AleReb/HIRI_ESTACIONARIO_CALEFACTOR/HIRI_STATIC_CALEFACTOR_0_1/serial_commands.ino

// -------------------- Serial Commands --------------------
// Sistema de comandos seriales para debug y mantenimiento
// Uso: Enviar comando por serial monitor (115200 baud, newline)
// Ejemplo: "help" → muestra lista de comandos

#include "config.h"

extern SystemConfig config;
extern TinyGsm modem;
extern RTC_DS3231 rtc;
extern Preferences prefs;
extern bool rtcOK;
extern bool SDOK;
extern bool loggingEnabled;
extern bool streaming;
extern bool oledOK;
extern uint32_t sendCounter;
extern uint32_t sdSaveCounter;
extern String csvFileName;
extern String rebootReason;
extern String networkOperator;
extern String networkTech;
extern String signalQuality;
extern String registrationStatus;
extern float batV;
extern int csq;
extern String gpsStatus;
extern String satellitesStr;
extern String hdopStr;
extern const char *DEVICE_ID_STR;
extern String VERSION;
extern String logFilePath;
extern String failedTxPath;

// Forward declarations
void saveConfig();
void configSetDefaults();
void printConfig();
void applyLEDConfig();
void clearSDCard();
void printSDInfo();
void printSDFileList();
String generateCSVFileName();
void writeCSVHeader();
bool syncRtcFromModem();      // Assuming implemented or needed
void resetModemSyncCounter(); // Assuming implemented or needed
bool getModemEpoch(uint32_t &epoch);

// Procesa comandos por puerto serie para operación, diagnóstico y mantenimiento.
// Permite inspección y control en campo sin recompilar firmware.
void processSerialCommand() {
  if (!Serial.available())
    return;

  String cmd = Serial.readStringUntil('\n');
  cmd.trim();
  cmd.toLowerCase();

  if (cmd.length() == 0)
    return;

  Serial.println("\n>>> Command: " + cmd);

  // -------------------- HELP --------------------
  if (cmd == "help" || cmd == "?") {
    Serial.println(F("=== HIRI PRO Serial Commands ==="));
    Serial.println(F("\n[RTC/Time]"));
    Serial.println(F("  rtc         - Show current RTC time"));
    Serial.println(F("  rtcsync     - Force sync RTC with modem"));
    Serial.println(F("  modemtime   - Show modem time only"));

    Serial.println(F("\n[Counters]"));
    Serial.println(F("  counters    - Show SD/HTTP counters"));
    Serial.println(F("  resetcnt    - Reset both counters to 0"));
    Serial.println(F("  stats       - Show detailed statistics"));

    Serial.println(F("\n[SD Card]"));
    Serial.println(F("  sdinfo      - Show SD card info"));
    Serial.println(F("  sdlist      - List files on SD"));
    Serial.println(F("  sdnew       - Create new CSV file"));
    Serial.println(
        F("  sdclear     - Delete all files on SD (WARNING: irreversible!)"));

    Serial.println(F("\n[Network/Modem]"));
    Serial.println(F("  netinfo     - Show network info"));
    Serial.println(F("  csq         - Show signal quality"));

    Serial.println(F("\n[System]"));
    Serial.println(F("  sysinfo     - Show system info"));
    Serial.println(F("  reboot      - Reboot ESP32"));
    Serial.println(F("  mem         - Show memory usage"));
    Serial.println(F("  cal <1-300> - Prueba el calefactor por N segundos (corte a 70 C)"));
    Serial.println(F("                 Ejemplo: cal 120"));

    Serial.println(F("\n[Streaming]"));
    Serial.println(F("  start       - Start streaming"));
    Serial.println(F("  stop        - Stop streaming"));

    Serial.println(F("\n[UI / OLED Flow]"));
    Serial.println(F("  Vista: Plantower / calefactor / sistema / GPS opcional"));
    Serial.println(F("  BTN1: prueba HTTP + SD + calefactor por 10 s"));
    Serial.println(F("  BTN2: siguiente vista (deshabilitado si BUTTON_PIN_2=-1)"));

    Serial.println(F("\n[Configuration]"));
    Serial.println(F("  config              - Show all configuration"));
    Serial.println(F("  config sd/http/display/power/system - Show specific config"));
    Serial.println(F("  set sdauto on/off   - Mount SD on boot"));
    Serial.println(F("  set sdsave 3/60/600/1200 - SD save period (seconds)"));
    Serial.println(F("  set httpsend 3/60/600/1200 - HTTP send period (seconds)"));
    Serial.println(F("  set httptimeout 5-30 - HTTP timeout (seconds)"));
    Serial.println(F("  set oledoff on/off  - OLED auto-off"));
    Serial.println(F("  set oledtime 60/120/180 - OLED timeout (seconds)"));
    Serial.println(F("  set led on/off      - Enable NeoPixel"));
    Serial.println(F("  set ledbright 10/25/50/100 - LED brightness (%)"));
    Serial.println(F("  set autostart on/off - Autostart streaming on boot"));
    Serial.println(F("  set gnss on/off     - Enable or disable GNSS subsystem"));
    Serial.println(F("  set autowaitgps on/off - Wait GPS fix before start"));
    Serial.println(
        F("  set autogpsto 60-900 - GPS timeout (60s-15min, default: 600s)"));
    Serial.println(F("  set rotatedisplay on/off - Rotate display 180 deg"));
    Serial.println(F("  set reboot 0-720   - Auto reboot hours (0 disables, default 3)"));
    Serial.println(
        F("  set gnssmode 1/3/5/7/15 - GNSS mode (1=GPS, 3=GPS+GLO, 15=ALL)"));
    Serial.println(F("  configreset         - Reset to defaults"));
    Serial.println(F("  configsave          - Save config to flash"));

    Serial.println(F("\n"));
  }

  // -------------------- HEATER COMMANDS --------------------
  else if (cmd.startsWith("cal ") || cmd.startsWith("cal.")) {
    String secondsText = cmd.substring(4);
    if (!heaterRequestTimedTest(secondsText)) {
      Serial.println(F("[CALEFACTOR] Uso: cal <1-300>. Ejemplo: cal 120"));
    }
  }

  // -------------------- RTC COMMANDS --------------------
  else if (cmd == "rtc") {
    if (!rtcOK) {
      Serial.println("[RTC] Not available");
      return;
    }
    DateTime now = rtc.now();
    Serial.printf("[RTC] Current time: %04d-%02d-%02d %02d:%02d:%02d\n",
                  now.year(), now.month(), now.day(), now.hour(), now.minute(),
                  now.second());
    Serial.printf("[RTC] Epoch: %lu\n", (unsigned long)now.unixtime());
    Serial.printf("[RTC] Temperature: %.2f°C\n", rtc.getTemperature());
    // Serial.printf("[RTC] Modem syncs: %u/3\n", rtcModemSyncCount);
  }  
  else if (cmd == "rtcsync") {
    if (!rtcOK) {
      Serial.println("[RTC] Not available");
      return;
    }
     Serial.printf("[RTC] Modem syncs: %u/3\n", rtcModemSyncCount);
    if (syncRtcFromModem()) {
      Serial.println("[RTC] ✓ Synced from modem");
    } else {
      Serial.println("[RTC] ✗ Sync failed");
    }
   
  }
  else if (cmd == "modemtime") {
    uint32_t epoch = 0;
    if (getModemEpoch(epoch)) {
      DateTime dt(epoch);
      Serial.printf("[MODEM] Current time: %04d-%02d-%02d %02d:%02d:%02d\n",
                    dt.year(), dt.month(), dt.day(), dt.hour(), dt.minute(), dt.second());
    } else {
      Serial.println("[MODEM] ✗ Failed to get time");
    }
  }

  // -------------------- COUNTER COMMANDS --------------------
  else if (cmd == "counters") {
    Serial.println("=== Counters ===");
    Serial.printf("SD saves:     %lu\n", (unsigned long)sdSaveCounter);
    Serial.printf("HTTP success: %lu\n", (unsigned long)sendCounter);
    if (sdSaveCounter > 0) {
      float successRate = (float)sendCounter / (float)sdSaveCounter * 100.0f;
      Serial.printf("Success rate: %.1f%%\n", successRate);
    }
  }

  else if (cmd == "resetcnt") {
    Serial.println("[COUNTERS] Resetting to 0...");
    sendCounter = 0;
    sdSaveCounter = 0;
    prefs.begin("system", false);
    prefs.putUInt("sendCnt", 0);
    prefs.putUInt("sdCnt", 0);
    prefs.end();
    Serial.println("[COUNTERS] ✓ Reset complete");
  }

  else if (cmd == "stats") {
    Serial.println("=== System Statistics ===");
    Serial.printf("Version:      %s\n", VERSION.c_str());
    Serial.printf("Device ID:    %s\n", DEVICE_ID_STR);
    Serial.printf("Uptime:       %lu s\n", millis() / 1000);
    Serial.printf("Streaming:    %s\n", streaming ? "ON" : "OFF");
    Serial.printf("SD logging:   %s\n", loggingEnabled ? "ON" : "OFF");
    Serial.printf("SD saves:     %lu\n", (unsigned long)sdSaveCounter);
    Serial.printf("HTTP success: %lu\n", (unsigned long)sendCounter);
    if (sdSaveCounter > 0) {
      float successRate = (float)sendCounter / (float)sdSaveCounter * 100.0f;
      Serial.printf("Success rate: %.1f%%\n", successRate);
    }
    Serial.printf("Battery:      %.2fV\n", batV);
    Serial.printf("CSQ:          %d\n", csq);
    Serial.printf("GPS:          %s\n", gpsStatus.c_str());
    Serial.printf("Satellites:   %s\n", satellitesStr.c_str());
    Serial.printf("HDOP:         %s\n", hdopStr.c_str());
    Serial.printf("Reboot reason:%s\n", rebootReason.c_str());
  }

  // -------------------- SD COMMANDS --------------------
  else if (cmd == "sdinfo") {
    printSDInfo();
  }

  else if (cmd == "sdlist") {
    printSDFileList();
  }

  else if (cmd == "sdnew") {
    if (!SDOK) {
      Serial.println("[SD] Not available");
      return;
    }
    Serial.println("[SD] Creating new CSV file...");
    csvFileName = generateCSVFileName();
    writeCSVHeader();
    Serial.printf("[SD] ✓ New file created: %s\n", csvFileName.c_str());
    // Persist new filename
    prefs.begin("system", false);
    prefs.putString("csvFile", csvFileName);
    prefs.end();
  }

  else if (cmd == "sdclear") {
    if (!SDOK) {
      Serial.println("[SD] Not available");
      return;
    }
    Serial.println(
        "[SD] ⚠ WARNING: This will delete ALL files on the SD card!");
    Serial.println("[SD] Type 'sdclear confirm' to proceed");
  }

  else if (cmd == "sdclear confirm") {
    clearSDCard();
  }

  // -------------------- NETWORK COMMANDS --------------------
  else if (cmd == "netinfo") {
    Serial.println("=== Network Info ===");
    Serial.printf("Operator:     %s\n", networkOperator.c_str());
    Serial.printf("Technology:   %s\n", networkTech.c_str());
    Serial.printf("CSQ:          %d\n", csq);
    Serial.printf("Registration: %s\n", registrationStatus.c_str());
    Serial.printf("PDP connected:%s\n", modem.isGprsConnected() ? "YES" : "NO");
    Serial.printf("Network conn: %s\n",
                  modem.isNetworkConnected() ? "YES" : "NO");
  }

  else if (cmd == "csq") {
    int newCsq = modem.getSignalQuality();
    Serial.printf("[MODEM] Signal Quality: %d", newCsq);
    if (newCsq == 0)
      Serial.println(" (no signal)");
    else if (newCsq < 10)
      Serial.println(" (marginal)");
    else if (newCsq < 15)
      Serial.println(" (ok)");
    else if (newCsq < 20)
      Serial.println(" (good)");
    else
      Serial.println(" (excellent)");
  }

  // -------------------- SYSTEM COMMANDS --------------------
  else if (cmd == "sysinfo") {
    Serial.println("=== System Info ===");
    Serial.printf("Firmware:     %s\n", VERSION.c_str());
    Serial.printf("Device ID:    %s\n", DEVICE_ID_STR);
    Serial.printf("Chip model:   %s\n", ESP.getChipModel());
    Serial.printf("Chip cores:   %d\n", ESP.getChipCores());
    Serial.printf("CPU freq:     %d MHz\n", ESP.getCpuFreqMHz());
    Serial.printf("Flash size:   %lu MB\n",
                  ESP.getFlashChipSize() / (1024 * 1024));
    Serial.printf("Free heap:    %lu bytes\n", ESP.getFreeHeap());
    Serial.printf("Uptime:       %lu s\n", millis() / 1000);
    if (config.scheduledRebootHours == 0) {
      Serial.println("Auto reboot:  OFF");
    } else {
      uint32_t uptimeS = millis() / 1000UL;
      uint32_t intervalS = (uint32_t)config.scheduledRebootHours * 3600UL;
      uint32_t remainingS = uptimeS < intervalS ? intervalS - uptimeS : 0;
      Serial.printf("Auto reboot:  every %u h, next in %lu s\n",
                    config.scheduledRebootHours, remainingS);
    }
    Serial.printf("Reboot reason:%s\n", rebootReason.c_str());
  }

  else if (cmd == "mem") {
    Serial.println("=== Memory Usage ===");
    Serial.printf("Free heap:    %lu bytes\n", ESP.getFreeHeap());
    Serial.printf("Heap size:    %lu bytes\n", ESP.getHeapSize());
    Serial.printf("Min free heap:%lu bytes\n", ESP.getMinFreeHeap());
    Serial.printf("Max alloc:    %lu bytes\n", ESP.getMaxAllocHeap());
  }

  else if (cmd == "reboot") {
    Serial.println("[SYSTEM] Rebooting in 2 seconds...");
    delay(2000);
    ESP.restart();
  }

  // -------------------- STREAMING COMMANDS --------------------
  else if (cmd == "start") {
    if (streaming) {
      Serial.println("[STREAM] Already running");
    } else {
      Serial.println("[STREAM] Starting via serial command...");
      streaming = true;
      // Etapa de integración: iniciar transmisión con logging OFF.
      loggingEnabled = false;
      Serial.printf("[STREAM] ✓ Started (SD logging: %s)\n",
                    loggingEnabled ? "ON" : "OFF");
    }
  }

  else if (cmd == "stop") {
    if (!streaming) {
      Serial.println("[STREAM] Already stopped");
    } else {
      Serial.println("[STREAM] Stopping...");
      streaming = false;
      loggingEnabled = false;
      Serial.println("[STREAM] ✓ Stopped");
    }
  }

  // -------------------- CONFIGURATION COMMANDS --------------------
  else if (cmd == "config") {
    printConfig();
  }

  else if (cmd == "config sd") {
    Serial.println("=== SD Configuration ===");
    Serial.printf("Auto-mount on boot: %s\n",
                  config.sdAutoMount ? "ON" : "OFF");
    Serial.printf("Save period:        %lu ms (%lu s)\n", config.sdSavePeriod,
                  config.sdSavePeriod / 1000);
  }

  else if (cmd == "config http") {
    Serial.println("=== HTTP Configuration ===");
    Serial.printf("Send period: %lu ms (%lu s)\n", config.httpSendPeriod,
                  config.httpSendPeriod / 1000);
    Serial.printf("Timeout:     %u seconds\n", config.httpTimeout);
  }

  else if (cmd == "config display") {
    Serial.println("=== Display Configuration ===");
    Serial.printf("Auto-off: %s\n", config.oledAutoOff ? "ON" : "OFF");
    Serial.printf("Timeout:  %lu ms (%lu s)\n", config.oledTimeout,
                  config.oledTimeout / 1000);
  }

  else if (cmd == "config power") {
    Serial.println("=== Power/LED Configuration ===");
    Serial.printf("NeoPixel enabled: %s\n", config.ledEnabled ? "YES" : "NO");
    Serial.printf("Brightness:       %u%%\n", config.ledBrightness);
  }

  else if (cmd == "config system") {
    Serial.println("=== System Configuration ===");
    Serial.printf("Rotate display:   %s\n", config.rotateDisplay ? "YES" : "NO");
    if (config.scheduledRebootHours == 0) {
      Serial.println("Scheduled reboot: OFF");
    } else {
      Serial.printf("Scheduled reboot: every %u hours\n",
                    config.scheduledRebootHours);
    }
  }

  else if (cmd.startsWith("set ")) {
    String param = cmd.substring(4);
    param.trim();

    // SD auto-mount
    if (param == "sdauto on") {
      config.sdAutoMount = true;
      saveConfig();
      Serial.println("[CONFIG] SD auto-mount: ON (will mount on next boot)");
    } else if (param == "sdauto off") {
      config.sdAutoMount = false;
      saveConfig();
      Serial.println("[CONFIG] SD auto-mount: OFF");
    }

    // SD save period
    else if (param == "sdsave 3") {
      config.sdSavePeriod = 3000;
      saveConfig();
      Serial.println("[CONFIG] SD save period: 3 seconds");
    } else if (param == "sdsave 60") {
      config.sdSavePeriod = 60000;
      saveConfig();
      Serial.println("[CONFIG] SD save period: 60 seconds");
    } else if (param == "sdsave 600") {
      config.sdSavePeriod = 600000;
      saveConfig();
      Serial.println("[CONFIG] SD save period: 600 seconds (10 min)");
    } else if (param == "sdsave 1200") {
      config.sdSavePeriod = 1200000;
      saveConfig();
      Serial.println("[CONFIG] SD save period: 1200 seconds (20 min)");
    }

    // HTTP send period
    else if (param == "httpsend 3") {
      config.httpSendPeriod = 3000;
      saveConfig();
      Serial.println("[CONFIG] HTTP send period: 3 seconds");
    } else if (param == "httpsend 60") {
      config.httpSendPeriod = 60000;
      saveConfig();
      Serial.println("[CONFIG] HTTP send period: 60 seconds");
    } else if (param == "httpsend 600") {
      config.httpSendPeriod = 600000;
      saveConfig();
      Serial.println("[CONFIG] HTTP send period: 600 seconds (10 min)");
    } else if (param == "httpsend 1200") {
      config.httpSendPeriod = 1200000;
      saveConfig();
      Serial.println("[CONFIG] HTTP send period: 1200 seconds (20 min)");
    }

    // HTTP timeout
    else if (param.startsWith("httptimeout ")) {
      int timeout = param.substring(12).toInt();
      if (timeout >= 5 && timeout <= 30) {
        config.httpTimeout = timeout;
        saveConfig();
        Serial.printf("[CONFIG] HTTP timeout: %d seconds\n", timeout);
      } else {
        Serial.println("[CONFIG] ✗ Timeout must be 5-30 seconds");
      }
    }

    // OLED auto-off
    else if (param == "oledoff on") {
      config.oledAutoOff = true;
      saveConfig();
      Serial.println("[CONFIG] OLED auto-off: ON");
    } else if (param == "oledoff off") {
      config.oledAutoOff = false;
      saveConfig();
      // Enable power
      // u8g2.setPowerSave(0); // Extern not available here directly, will
      // handle loop
      Serial.println("[CONFIG] OLED auto-off: OFF (always on)");
    }

    // OLED timeout
    else if (param == "oledtime 60") {
      config.oledTimeout = 60000;
      saveConfig();
      Serial.println("[CONFIG] OLED timeout: 60 seconds");
    } else if (param == "oledtime 120") {
      config.oledTimeout = 120000;
      saveConfig();
      Serial.println("[CONFIG] OLED timeout: 120 seconds (2 min)");
    } else if (param == "oledtime 180") {
      config.oledTimeout = 180000;
      saveConfig();
      Serial.println("[CONFIG] OLED timeout: 180 seconds (3 min)");
    }

    // LED enable/disable
    else if (param == "led on") {
      config.ledEnabled = true;
      saveConfig();
      applyLEDConfig();
      Serial.println("[CONFIG] NeoPixel: ON");
    } else if (param == "led off") {
      config.ledEnabled = false;
      saveConfig();
      applyLEDConfig();
      Serial.println("[CONFIG] NeoPixel: OFF");
    }

    // LED brightness
    else if (param == "ledbright 10") {
      config.ledBrightness = 10;
      saveConfig();
      applyLEDConfig();
      Serial.println("[CONFIG] LED brightness: 10%");
    } else if (param == "ledbright 25") {
      config.ledBrightness = 25;
      saveConfig();
      applyLEDConfig();
      Serial.println("[CONFIG] LED brightness: 25%");
    } else if (param == "ledbright 50") {
      config.ledBrightness = 50;
      saveConfig();
      applyLEDConfig();
      Serial.println("[CONFIG] LED brightness: 50%");
    } else if (param == "ledbright 100") {
      config.ledBrightness = 100;
      saveConfig();
      applyLEDConfig();
      Serial.println("[CONFIG] LED brightness: 100%");
    }

    // Autostart
    else if (param == "autostart on") {
      config.autostart = true;
      saveConfig();
      Serial.println("[CONFIG] Autostart: ON (will start on next boot)");
    } else if (param == "autostart off") {
      config.autostart = false;
      saveConfig();
      Serial.println("[CONFIG] Autostart: OFF");
    }

    else if (param == "gnss on") {
      config.gnssEnabled = true;
      saveConfig();
      Serial.println("[CONFIG] GNSS: ON (requires reboot)");
    } else if (param == "gnss off") {
      config.gnssEnabled = false;
      saveConfig();
      Serial.println("[CONFIG] GNSS: OFF (requires reboot)");
    }

    // Autostart wait GPS
    else if (param == "autowaitgps on") {
      config.autostartWaitGps = true;
      saveConfig();
      Serial.println("[CONFIG] Autostart wait GPS: ON (will wait for fix)");
    } else if (param == "autowaitgps off") {
      config.autostartWaitGps = false;
      saveConfig();
      Serial.println("[CONFIG] Autostart wait GPS: OFF");
    }

    // Autostart GPS timeout
    else if (param.startsWith("autogpsto ")) {
      int val = param.substring(10).toInt();
      if (val >= 60 && val <= 900) {
        config.autostartGpsTimeout = val;
        saveConfig();
        Serial.printf("[CONFIG] Autostart GPS timeout: %u seconds (%u min)\n",
                      val, val / 60);
      } else {
        Serial.println(
            "[CONFIG] ✗ Invalid timeout (must be 60-900 seconds / 1-15 min)");
      }
    }

    // Rotate display
    else if (param == "rotatedisplay on") {
      config.rotateDisplay = true;
      saveConfig();
      if (oledOK) u8g2.setDisplayRotation(U8G2_R0);
      Serial.println("[CONFIG] Rotate Display: ON");
    } else if (param == "rotatedisplay off") {
      config.rotateDisplay = false;
      saveConfig();
      if (oledOK) u8g2.setDisplayRotation(U8G2_R2);
      Serial.println("[CONFIG] Rotate Display: OFF");
    }

    // Scheduled reboot
    else if (param.startsWith("reboot ")) {
      String valStr = param.substring(7);
      valStr.trim();
      bool numeric = valStr.length() > 0;
      for (size_t i = 0; i < valStr.length(); ++i) {
        if (!isDigit(valStr[i])) {
          numeric = false;
          break;
        }
      }

      int val = numeric ? valStr.toInt() : -1;
      if (val >= 0 && val <= 720) {
        config.scheduledRebootHours = (uint16_t)val;
        saveConfig();
        if (val == 0) {
          Serial.println("[CONFIG] Scheduled reboot: OFF");
        } else {
          Serial.printf("[CONFIG] Scheduled reboot: every %d hours\n", val);
        }
      } else {
        Serial.println("[CONFIG] Invalid reboot value (use 0-720 hours)");
      }
    }

    // GNSS mode
    else if (param.startsWith("gnssmode ")) {
      int val = param.substring(9).toInt();
      if (val == 1 || val == 3 || val == 5 || val == 7 || val == 15) {
        config.gnssMode = val;
        saveConfig();
        Serial.print("[CONFIG] GNSS mode: ");
        Serial.print(val);
        Serial.println(" (Requires Reboot)");
      } else {
        Serial.println("[CONFIG] ✗ Invalid mode (valid: 1, 3, 5, 7, 15)");
      }
    }

    else {
      Serial.println("[CONFIG] ✗ Unknown parameter. Type 'help' for list.");
    }
  }

  else if (cmd == "configreset") {
    Serial.println("[CONFIG] Resetting to defaults...");
    configSetDefaults();
    saveConfig();
    applyLEDConfig();
    Serial.println("[CONFIG] ✓ Reset complete. Reboot to apply all changes.");
  }

  else if (cmd == "configsave") {
    saveConfig();
  }

  // -------------------- UNKNOWN COMMAND --------------------
  else {
    Serial.println("[CMD] Unknown command. Type 'help' for list.");
  }

  Serial.println();
}
