AleReb/HIRI_ESTACIONARIO_CALEFACTOR/codigo_original/dfrobot_plantower_SD_sim7600V7/tipo.h

/*
  Fontname: -FontForge-MissingPlanet-Medium-R-Normal--72-690-75-75-P-272-ISO10646-1
  Copyright: Extant
  Glyphs: 91/423
  BBX Build Mode: 0
*/
const uint8_t MissingPlanet72[2692] U8G2_FONT_SECTION("MissingPlanet72") =
  "[\0\5\4\6\6\5\6\7\62\77\367\356)\356)\0\3\322\10+\12g \6\0\0\303+!\14E"
  "\12\301$\370\377\200\242\17(\42\13\216\3w)(D\377\37)#ZW\12\301-\251R!%\25R"
  "R!%\25RR!%\25RR!%\25R\312\3\377\1E\252THI\205\224THI\205\224T"
  "HI\205\224THI\205\224THI\205\224THI\205\224\362\300\177@\221*\25RR!%\25R"
  "R!%\25RR!%\25RR!\245\0$V\227\14\267m*\262\226\36\370\37)\251\220\222\12)"
  "\251\220\222\12)\251\220\222\12)\251\220\222\12)\251\220\222\12)\251\220\222\12)\351\201\377\200J\205\224"
  "THI\205\224THI\205\224THI\205\224THI\205\224THI\205\224THI\205<\360\277"
  "Td]\2%TW\12\301-p\344\1B\36 \344\1B\36 D\221B\24)D\221B\24)\344"
  "\1B\36 \344\1B\36 \344\1BJ+\262\346\222+\262\326\212\254\271\7\32y\200\220\7\10y\200"
  "\220\7\10)D\221B\24)D\221B\24y\200\220\7\10y\200\220\7\10q&p`\12A\62x\0"
  "\245\7Pz\0\245\7Pz\0\245\322J*\255\244\322J*\255\244\322J*\255\244\322J*\255\244\322"
  "*Rd!E\26Rd!E\272T\265\222J+\251\264\222J+\244\226\12\251R!U*\244*\211"
  "\270RZI\245\225TZI\245\225TP!\245\24TH)\5\25RJA\205\224\362\300 \17\244\366"
  "\0i\17\220\366\0i\5'\11\205\3\367$\370\3\12(\21N\12A)\370\227\352\377\377\377K\17\374"
  "\200\2)\21N\12A)\370\3*\325\377\377\377\227\36\370\3*(\327\5\345-(\244\20E\12Q\244"
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
                        "<path d=\"M34.9963 17.4999C35.0232 18.5207 34.5611 19.7478 33.7153 20.5936C32.8695 21.4394 31.6424 21.9015 30.6217 21.8746C29.6009 21.9015 28.3738 21.4394 27.528 20.5936C26.6822 19.7478 26.2201 18.5207 26.247 17.4999C26.2201 16.4792 26.6822 15.2522 27.528 14.4064C28.3738 13.5606 29.6009 13.0984 30.6217 13.1253C31.6424 13.0984 32.8695 13.5606 33.7153 14.4064C34.5611 15.2522 35.0232 16.4792 34.9963 17.4999Z\" fill=\"#27273F\"/>"
                        "</svg>";
